LaskaKit/ESP32-DEVKit/img/LaskaKit-ESP32-DEVKit_v2-2.jpg

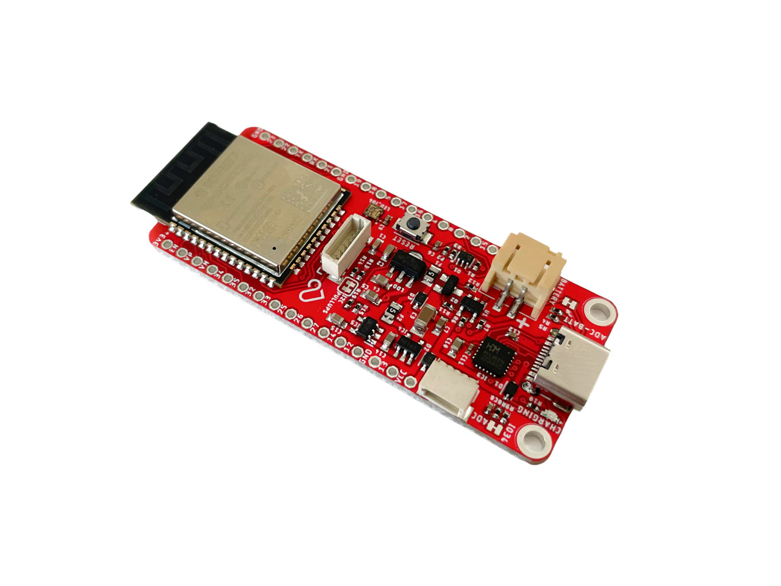
img/LaskaKit-ESP32-DEVKit_v2-2.jpg
